illness072/elephant42/cases/v1/hanger-R.stl

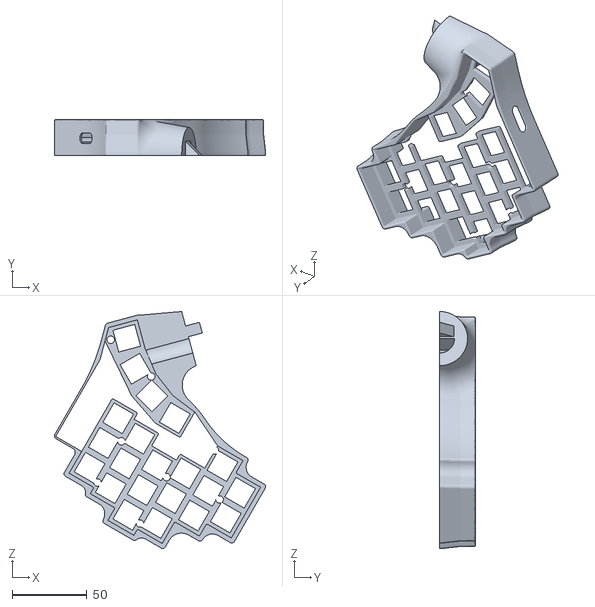
[picture p18: CAD file, 2020-07-06, an earlier design]
cases/v1/hanger-R.stl
140.9 x 24.0 x 158.1
