illness072/elephant42/docs/build-guide/remap-select.jpeg

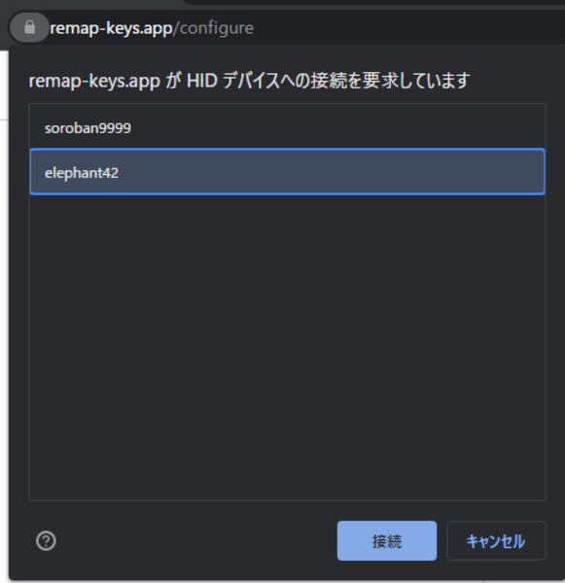
docs/build-guide/remap-select.jpeg
