illness072/elephant42/docs/build-guide/remap-write0.jpeg

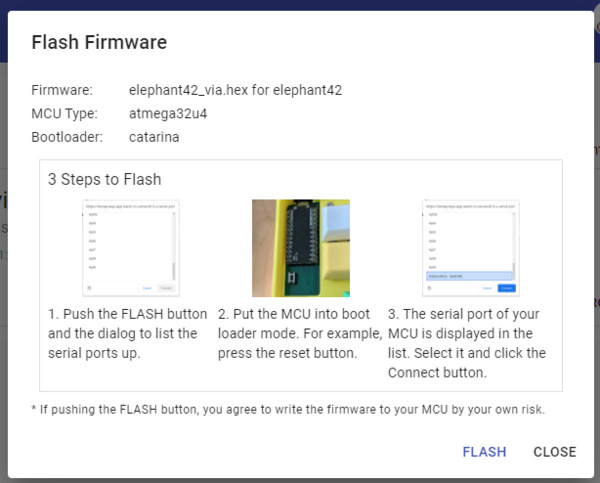
docs/build-guide/remap-write0.jpeg
